jdc-cunningham/bl-monocle-stuff/3d-printing/phone-hand-held-monocle-mount/stls/rotating-paddle.stl

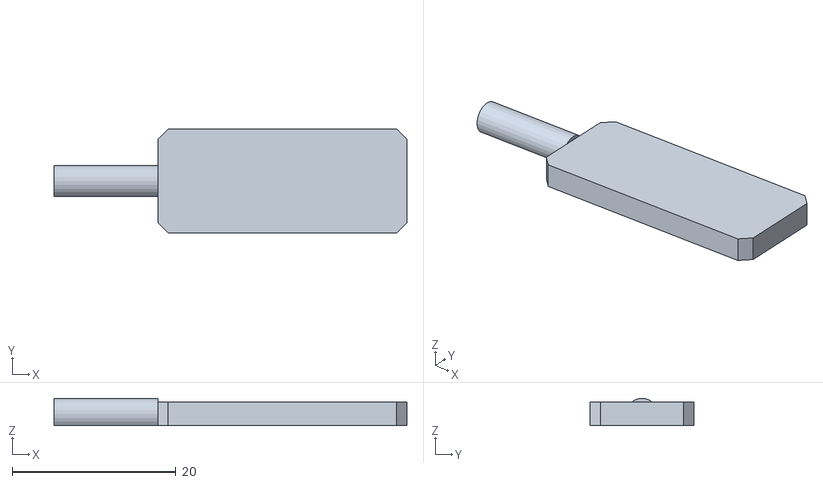
[picture p20: CAD file, 2023-03-25]
3d-printing/phone-hand-held-monocle-mount/stls/rotating-paddle.stl
43.2 x 12.7 x 3.35
