jdc-cunningham/bl-monocle-stuff/3d-printing/phone-recording-stand/stls/monocle-sliding-pivot-mount.stl

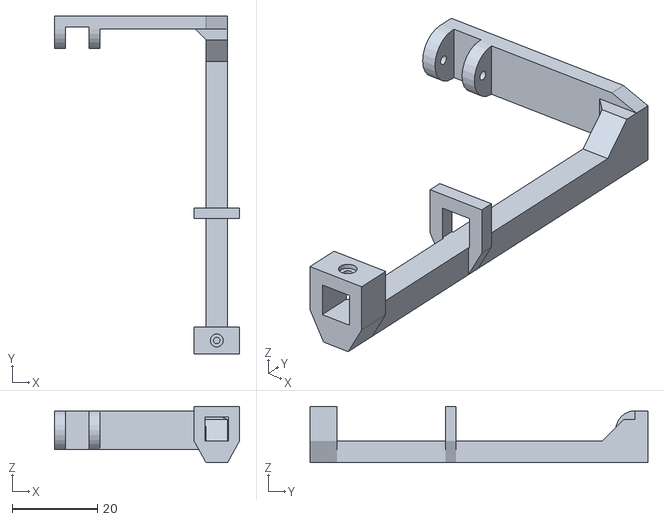
[picture p21: CAD file, 2023-03-04]
3d-printing/phone-recording-stand/stls/monocle-sliding-pivot-mount.stl
43.4 x 79.2 x 13.2
