jdc-cunningham/bl-monocle-stuff/3d-printing/simone-pi-zero-case/print/pz-batt-case--both.stl

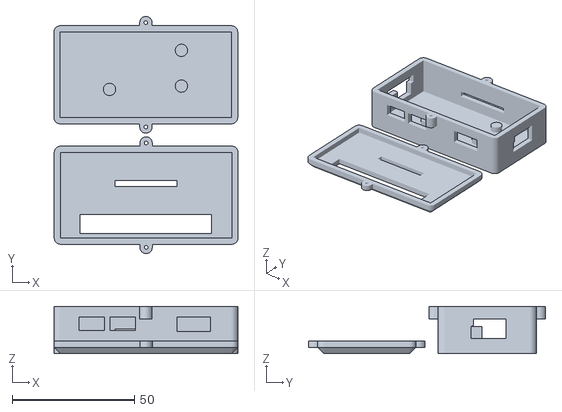
[picture p22: CAD file, 2023-03-30]
3d-printing/simone-pi-zero-case/print/pz-batt-case--both.stl
75.2 x 97.0 x 19.3
