jdc-cunningham/bl-monocle-stuff/3d-printing/glasses-permanent-clip/test-magnet-holder.stl

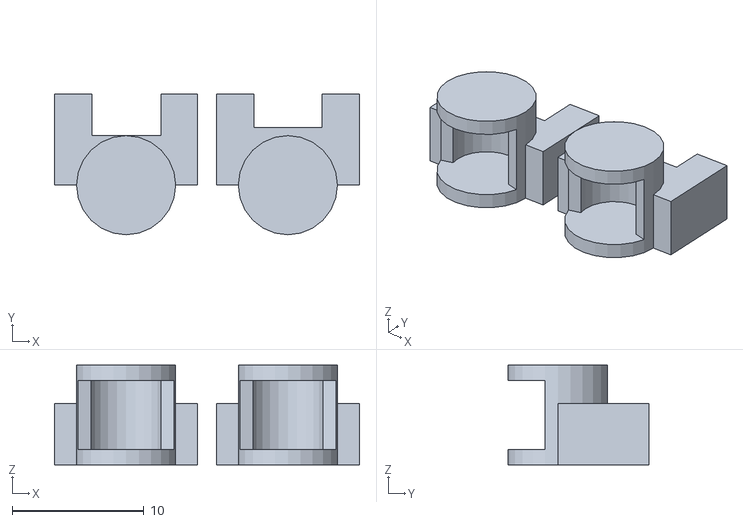
[picture p23: CAD file, 2023-05-14]
3d-printing/glasses-permanent-clip/test-magnet-holder.stl
23.1 x 10.7 x 7.54
