jdc-cunningham/bl-monocle-stuff/3d-printing/phone-recording-stand/stls/monocle-phone-holder.stl

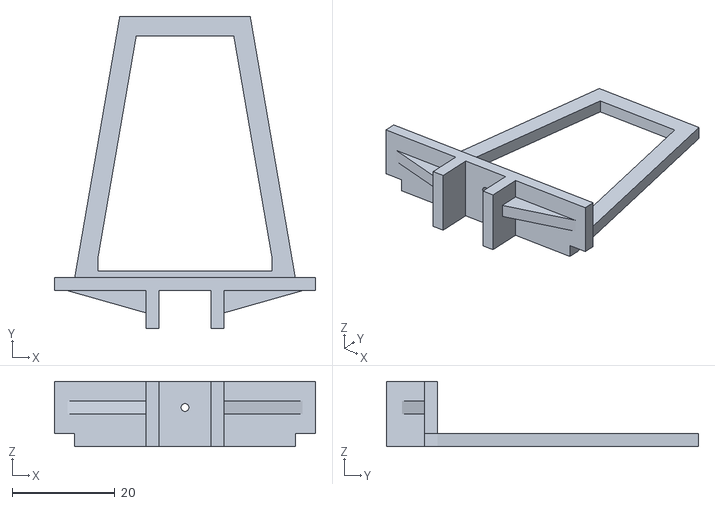
[picture p24: CAD file, 2023-03-02]
3d-printing/phone-recording-stand/stls/monocle-phone-holder.stl
50.8 x 60.7 x 12.7
