jdc-cunningham/bl-monocle-stuff/3d-printing/phone-recording-stand/stls/monocle-stand--base.stl

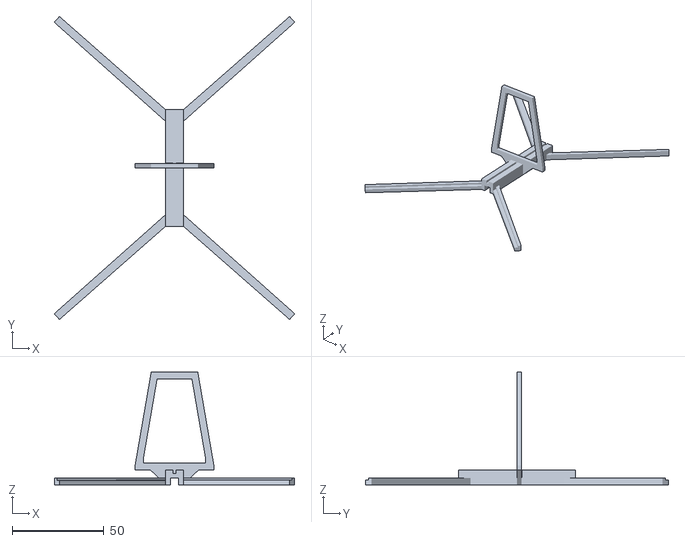
[picture p25: CAD file, 2023-03-02]
3d-printing/phone-recording-stand/stls/monocle-stand--base.stl
131.0 x 165.1 x 61.5
