jdc-cunningham/bl-monocle-stuff/3d-printing/phone-recording-stand/stls/monocle-holder.stl

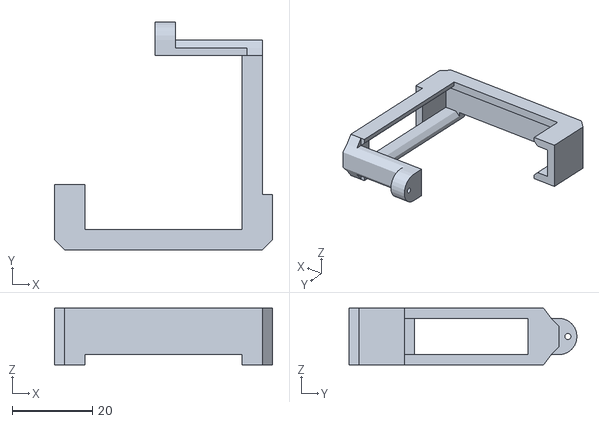
[picture p26: CAD file, 2023-03-02]
3d-printing/phone-recording-stand/stls/monocle-holder.stl
54.4 x 56.9 x 14.2
